Kowitzki/Rear-Wheeled-Bobbycar/Pictures/200107500293_56961.jpg

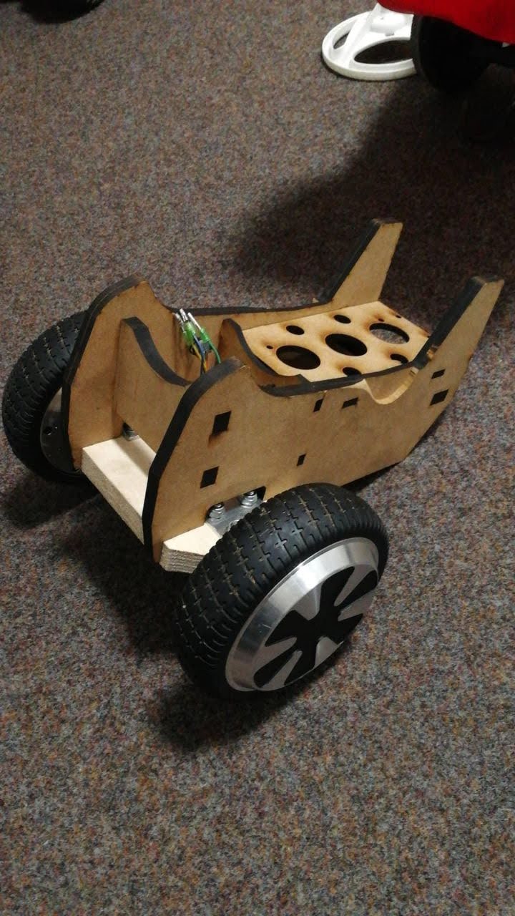
Pictures/200107500293_56961.jpg
