Kowitzki/Rear-Wheeled-Bobbycar/Pictures/200171600913_39799.jpg

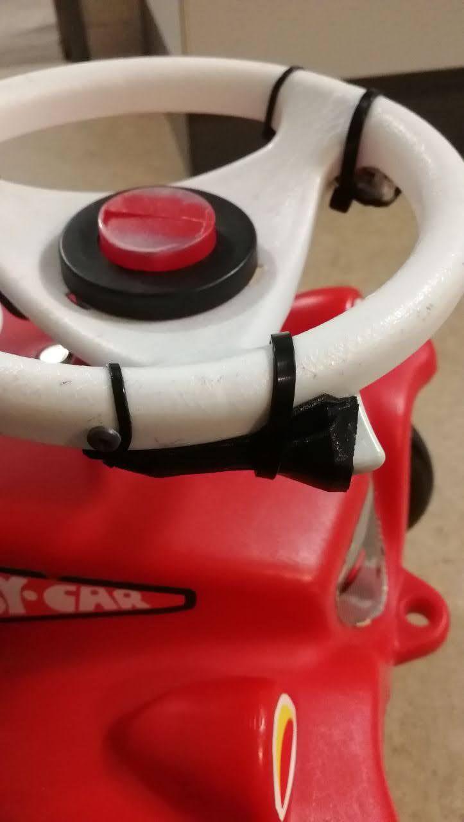
Pictures/200171600913_39799.jpg
