Kowitzki/Rear-Wheeled-Bobbycar/Pictures/IMG_20200920_234603_898.jpg

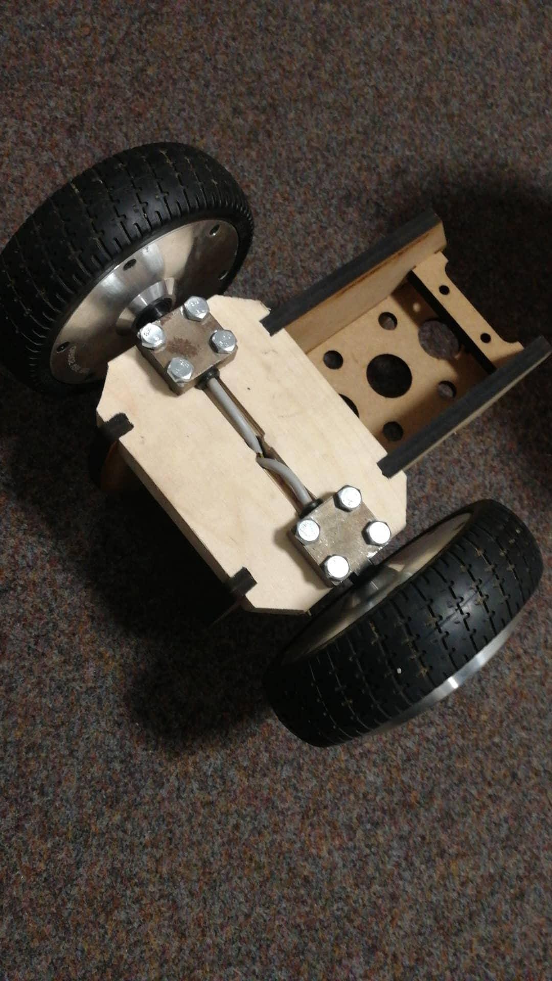
Pictures/IMG_20200920_234603_898.jpg
