Kowitzki/Rear-Wheeled-Bobbycar/Pictures/IMG_20201227_195217.jpg

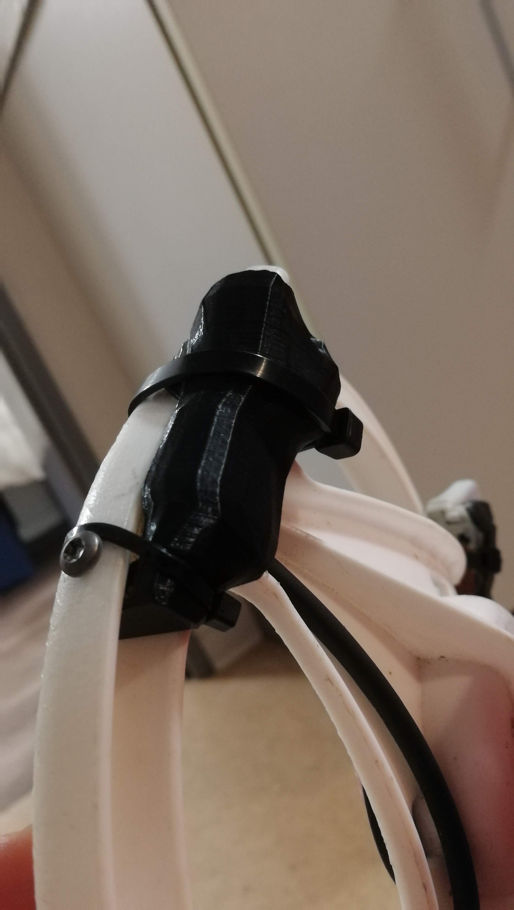
Pictures/IMG_20201227_195217.jpg
