Kowitzki/Rear-Wheeled-Bobbycar/PrintedParts/AkkuDeckel.stl

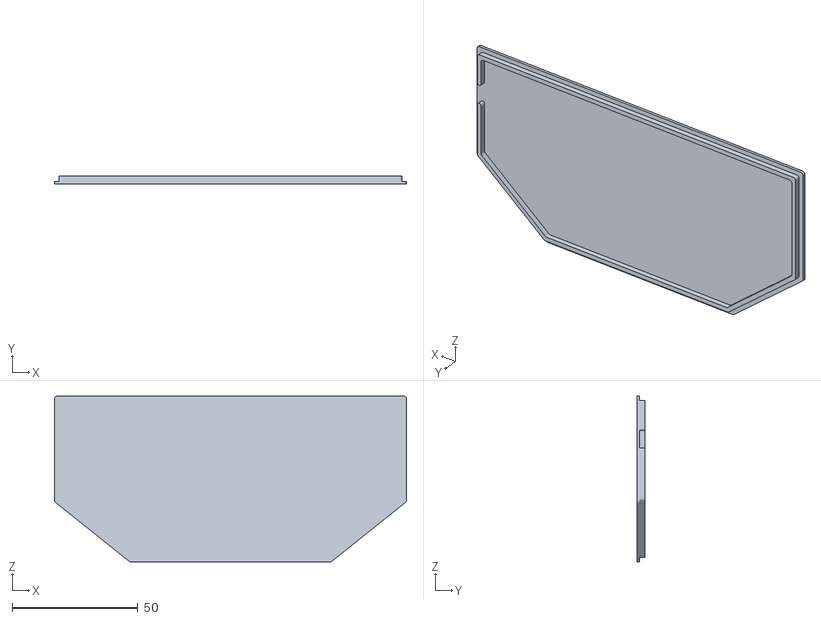
[picture p22: CAD file, 2021-08-03]
PrintedParts/AkkuDeckel.stl
140.0 x 3.00 x 66.0
