Kowitzki/Rear-Wheeled-Bobbycar/DxfWood/Akkubefestigung.dxf

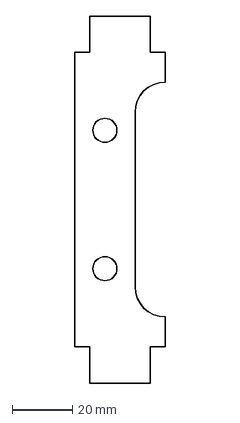
[picture p23: CAD file, 2021-08-03]
DxfWood/Akkubefestigung.dxf
30.0 x 122.0 mm
