Kowitzki/Rear-Wheeled-Bobbycar/PrintedParts/AkkuKörperMirr.stl

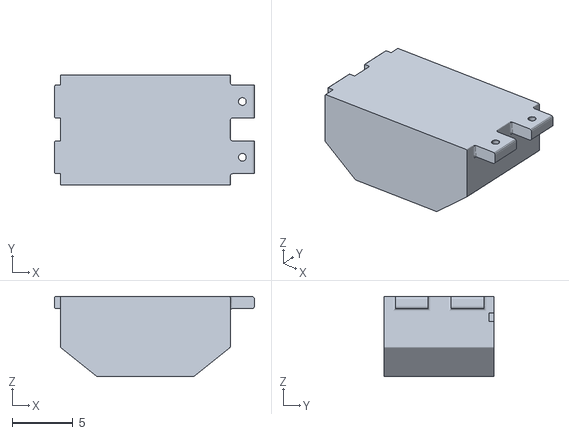
[picture p24: CAD file, 2021-08-03]
PrintedParts/AkkuKörperMirr.stl
16.5 x 9.10 x 6.60
