Kowitzki/Rear-Wheeled-Bobbycar/PrintedParts/PVC_Adapter_Gummi.stl

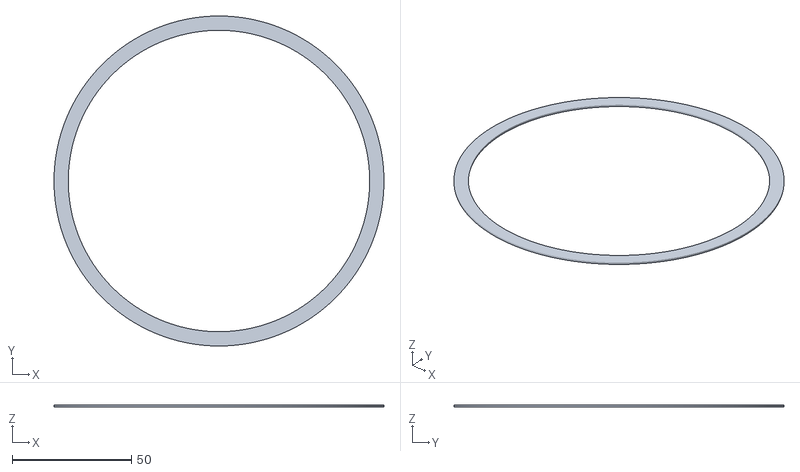
[picture p25: CAD file, 2021-08-03]
PrintedParts/PVC_Adapter_Gummi.stl
138.3 x 138.3 x 0.9
